DutchMaker/TTL-computer/Circuits/Breadboards/Clock.jpg

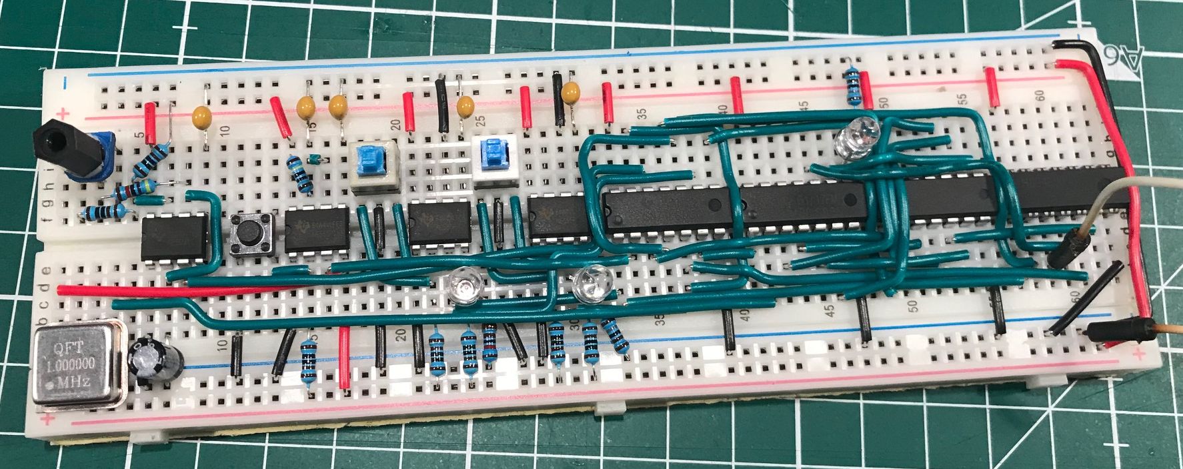
Circuits/Breadboards/Clock.jpg
