DutchMaker/TTL-computer/Circuits/Pictures/Clock.jpg

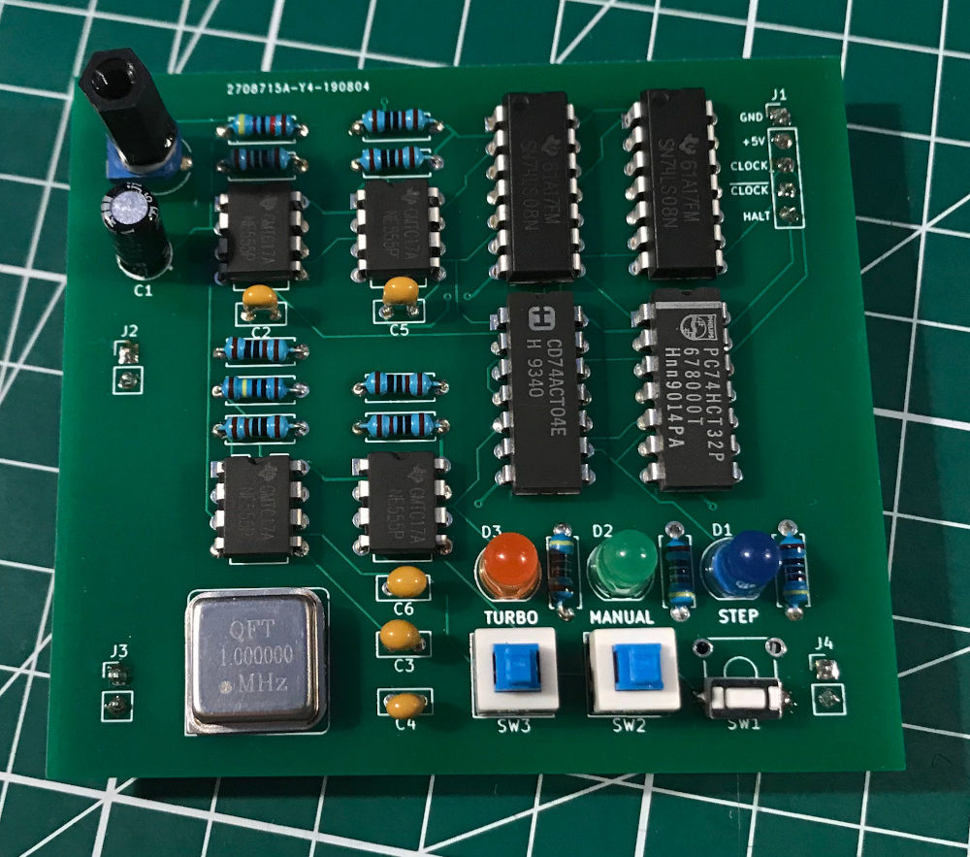
Circuits/Pictures/Clock.jpg
