DutchMaker/TTL-computer/Circuits/Pictures/Controller.jpg

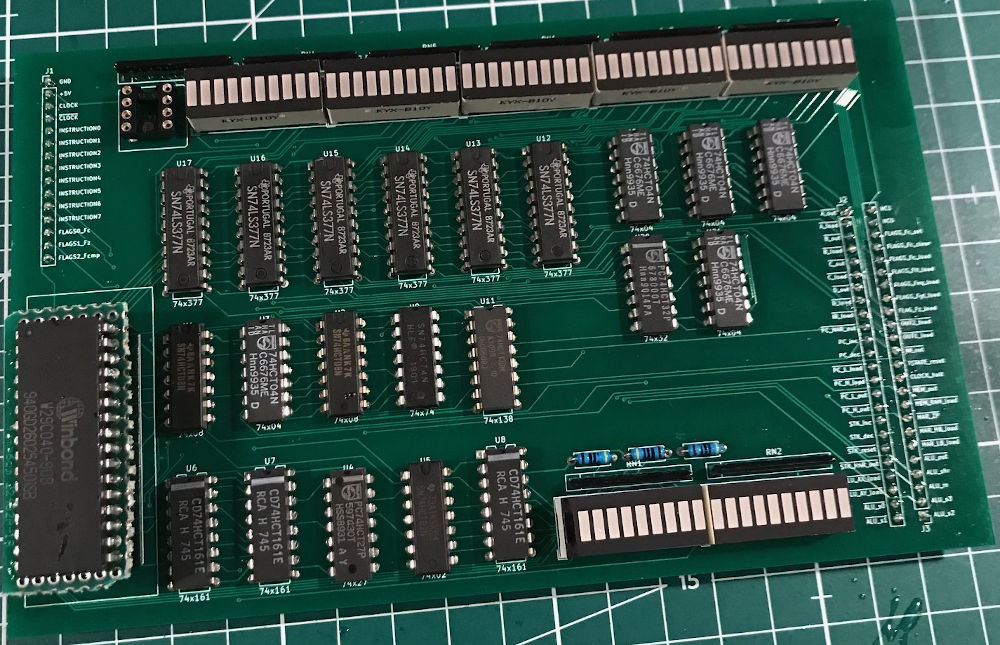
Circuits/Pictures/Controller.jpg
