DutchMaker/TTL-computer/Circuits/Pictures/Memory.jpg

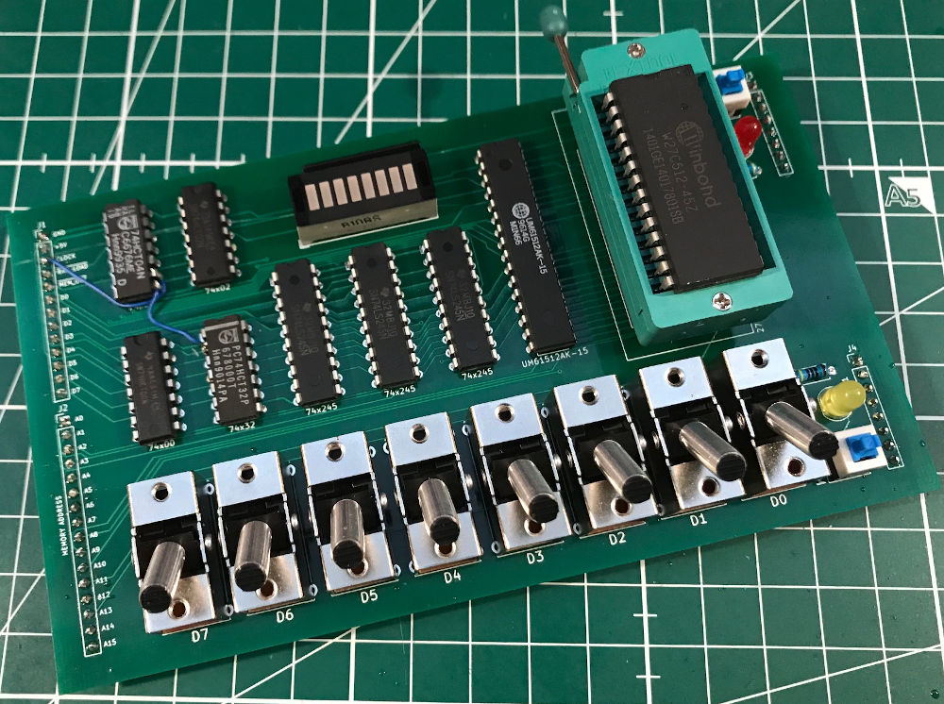
Circuits/Pictures/Memory.jpg
