DutchMaker/TTL-computer/Circuits/Pictures/Stack-Pointer.jpg

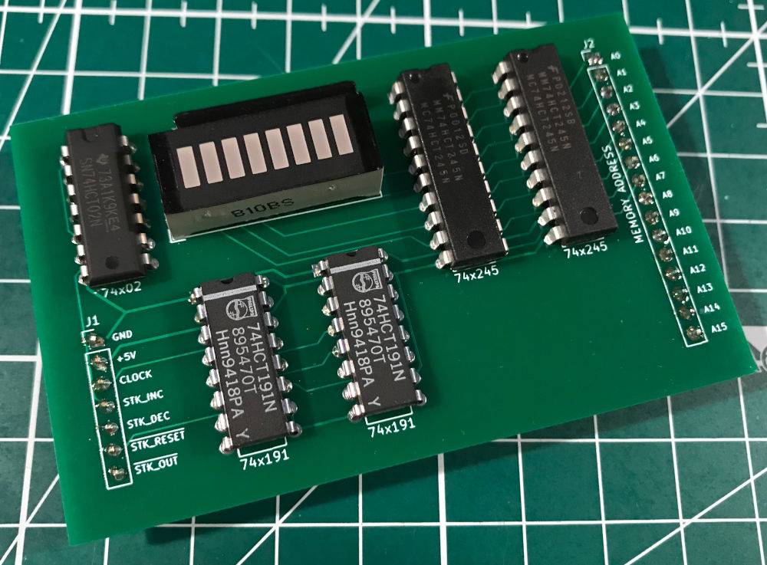
Circuits/Pictures/Stack-Pointer.jpg
