DutchMaker/TTL-computer/Documentation/Datasheets/74181-operations.png

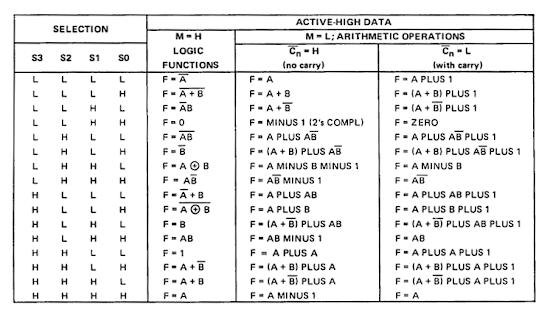
Documentation/Datasheets/74181-operations.png
