DutchMaker/TTL-computer/Circuits/PDF/Register.pdf

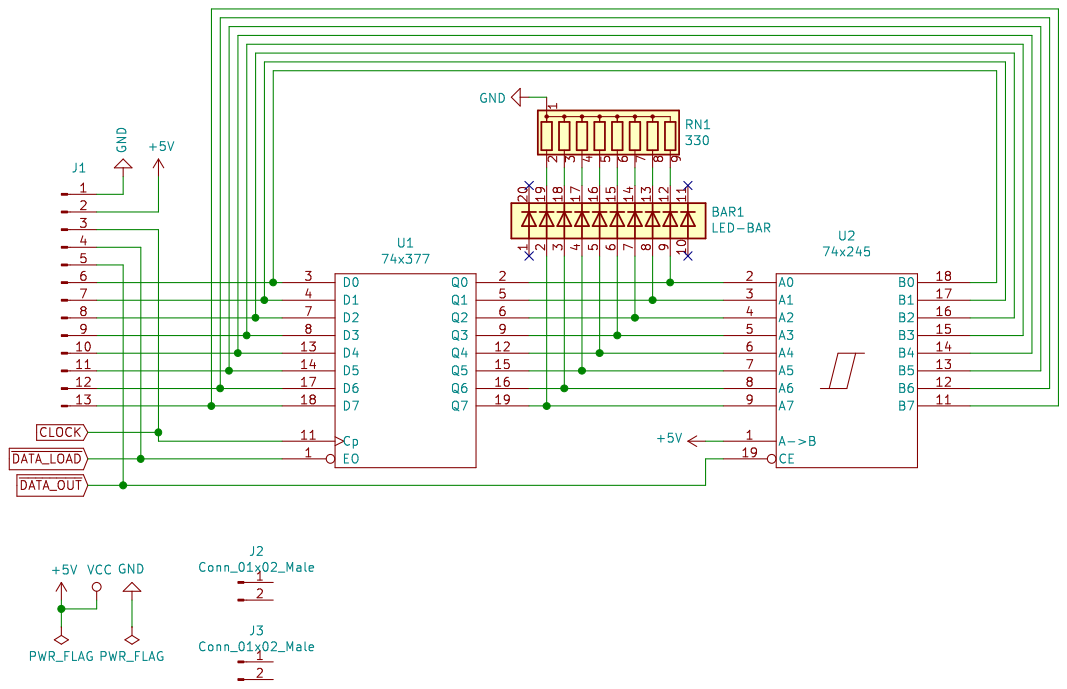
[picture p37: page 1]
