DutchMaker/TTL-computer/Circuits/PDF/Stack-Pointer.pdf

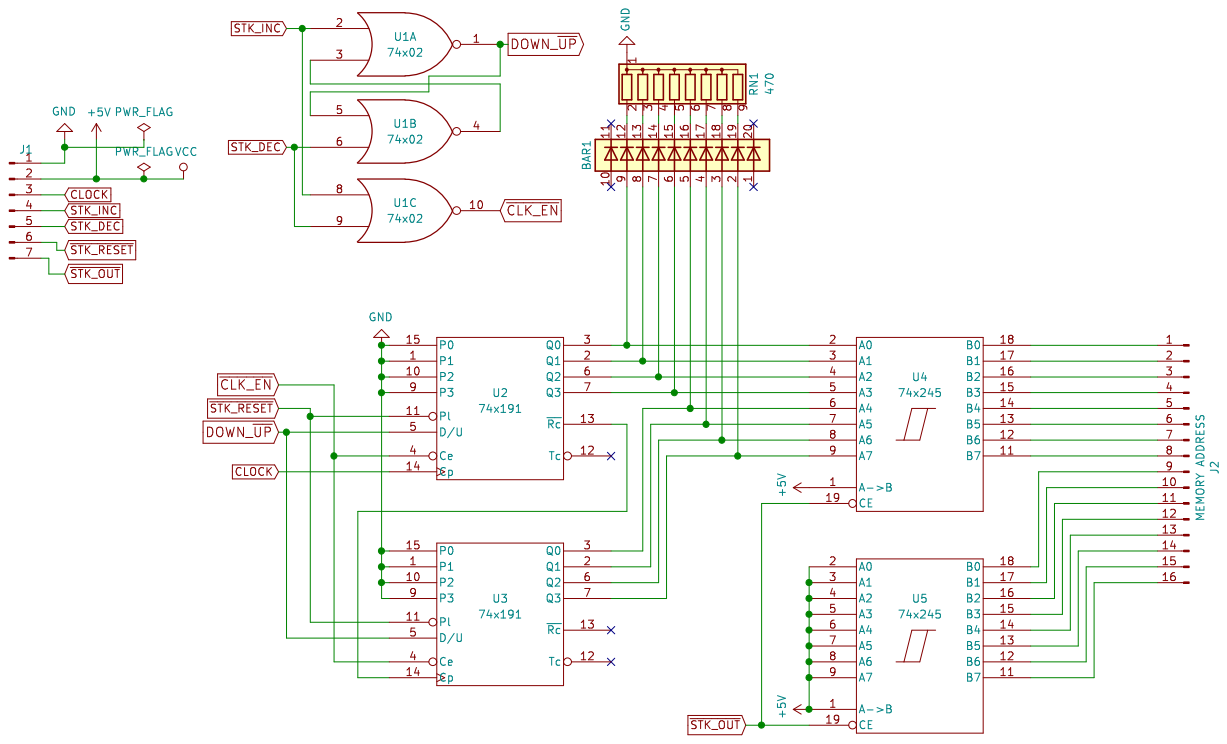
[picture p38: page 1]
